loco-lab/hera-led/Solidworks_Assembly/Top Layer.SLDPRT

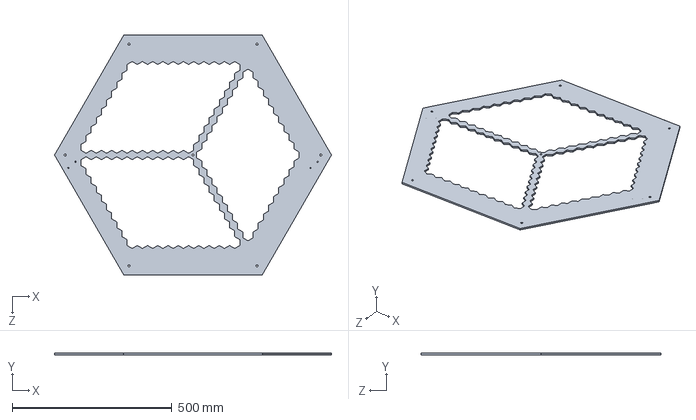
[picture p19: CAD file, 2019-11-21]
Solidworks_Assembly/Top Layer.SLDPRT
866.0 x 4.76 x 750.0 mm
