loco-lab/hera-led/Solidworks_Assembly/6-32 x 0.75in Screw Assy.SLDASM

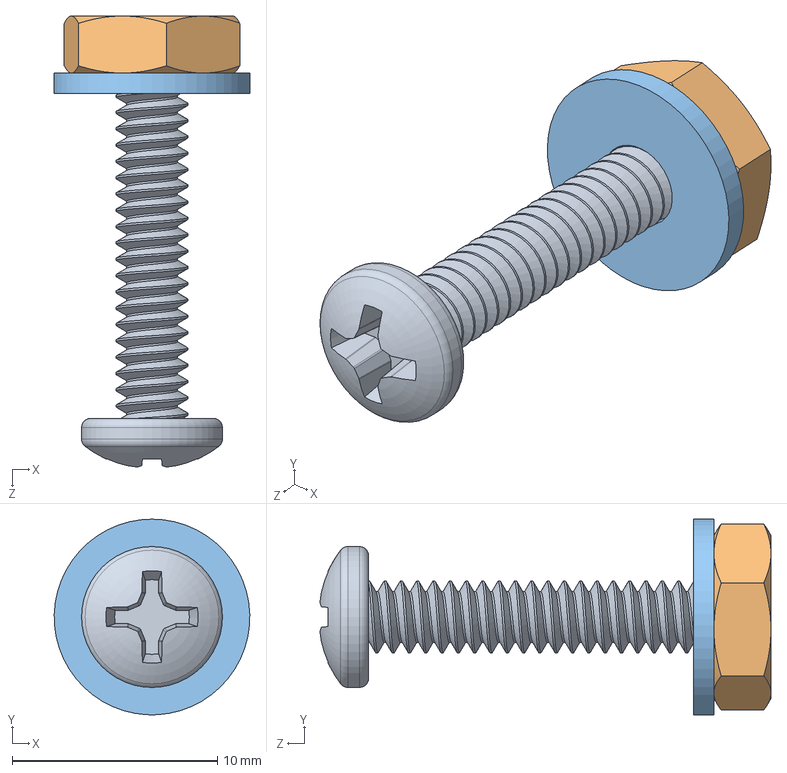
[picture p20: CAD file, 2019-11-21]
Solidworks_Assembly/6-32 x 0.75in Screw Assy.SLDASM
9.52 x 9.53 x 21.9 mm
6-32 x 0.75in Screw
6-32 Nut
6-32 Washer
