loco-lab/hera-led/HERAtest.py

#!/usr/bin/env python3
#Author: Mickey Horn
#custom code testing for HERA LED model

import time
from neopixel import *
import argparse
import pandas as pd
import numpy as np
from datetime import datetime
import math
import random
import matplotlib.pyplot as plt
import matplotlib.colors as clr
import urllib2

parser = argparse.ArgumentParser()
parser.add_argument('-c', '--clear', action='store_true', help='clear the display on exit')
args = parser.parse_args()

# LED strip configuration:
LED_COUNT      = 320     # Number of LED pixels.
LED_PIN        = 18      # GPIO pin connected to the pixels (18 uses PWM!).
LED_FREQ_HZ    = 800000  # LED signal frequency in hertz (usually 800khz)
LED_DMA        = 10      # DMA channel to use for generating signal (try 10)
LED_BRIGHTNESS = 55     # Set to 0 for darkest and 255 for brightest
LED_INVERT     = False   # True to invert the signal (when using NPN transistor level shift)
LED_CHANNEL    = 0       # set to '1' for GPIOs 13, 19, 41, 45 or 53

# Correlates the antenna number defined by HERA to the LED number in the sequential string. Antenna#:LED#
scheme = {
    0:10, 1:9, 2:8, 3:7, 4:6, 5:5, 6:4, 7:3, 8:2, 9:1, 10:0,
    11:11, 12:12, 13:13, 14:14, 15:15, 16:16, 17:17, 18:18, 19:19, 20:20, 21:21,
    22:119,
    23:32, 24:31, 25:30, 26:29, 27:28, 28:27, 29:26, 30:25, 31:24, 32:23, 33:22,
    34:118, 35:120,
    36:33, 37:34, 38:35, 39:36, 40:37, 41:38, 42:39, 43:40, 44:41, 45:42, 46:43,
    47:117, 48:121, 49:139,
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

sec_ring = [214,213,212,211,210,209,208,207,206,205,204,203,202,201,200,199,180,179,160,159,140,139,120,119,0,1,2,3,4,5,6,7,8,9,10,11,32,33,54,55,76,77,98,99,309,308,287,286,265,264,243,242,221,220,219,218,217,216,215]

hours_dict = { # correlates the hour with the hour hand position
    '00':hourhand12, '12':hourhand12,
    '01':hourhand01, '13':hourhand01,
    '02':hourhand02, '14':hourhand02,
    '03':hourhand03, '15':hourhand03,
    '04':hourhand04, '16':hourhand04,
    '05':hourhand05, '17':hourhand05,
    '06':hourhand06, '18':hourhand06,
    '07':hourhand07, '19':hourhand07,
    '08':hourhand08, '20':hourhand08,
    '09':hourhand09, '21':hourhand09,
    '10':hourhand10, '22':hourhand10,
    '11':hourhand11, '23':hourhand11
}

mins_dict = { # correlates the minute with the hour/minute hand position
    '00':hourhand12, '01':hourhand12, '02':hourhand12, '03':hourhand12, '04':hourhand12,
    '05':hourhand01, '06':hourhand01, '07':hourhand01, '08':hourhand01, '09':hourhand01,
    '10':hourhand02, '11':hourhand02, '12':hourhand02, '13':hourhand02, '14':hourhand02,
    '15':hourhand03, '16':hourhand03, '17':hourhand03, '18':hourhand03, '19':hourhand03,
    '20':hourhand04, '21':hourhand04, '22':hourhand04, '23':hourhand04, '24':hourhand04,
    '25':hourhand05, '26':hourhand05, '27':hourhand05, '28':hourhand05, '29':hourhand05,
    '30':hourhand06, '31':hourhand06, '32':hourhand06, '33':hourhand06, '34':hourhand06,
    '35':hourhand07, '36':hourhand07, '37':hourhand07, '38':hourhand07, '39':hourhand07,
    '40':hourhand08, '41':hourhand08, '42':hourhand08, '43':hourhand08, '44':hourhand08,
    '45':hourhand09, '46':hourhand09, '47':hourhand09, '48':hourhand09, '49':hourhand09,
    '50':hourhand10, '51':hourhand10, '52':hourhand10, '53':hourhand10, '54':hourhand10,
    '55':hourhand11, '56':hourhand11, '57':hourhand11, '58':hourhand11, '59':hourhand11
}

secs_dict = { # correlates the second with a point on the edge
    '00':214, '01':213, '02':212, '03':211, '04':210,
    '05':209, '06':208, '07':207, '08':206, '09':205,
    '10':204, '11':203, '12':202, '13':201, '14':200,
    '15':199, '16':180, '17':179, '18':160, '19':159,
    '20':140, '21':139, '22':120, '23':119, '24':0,
    '25':1, '26':2, '27':3, '28':4, '29':5,
    '30':6, '31':7, '32':8, '33':9, '34':10,
    '35':11, '36':32, '37':33, '38':54, '39':55,
    '40':76, '41':77, '42':98, '43':99, '44':309,
    '45':308, '46':287, '47':286, '48':265, '49':264,
    '50':243, '51':242, '52':221, '53':220, '54':219,
    '55':218, '56':217, '57':216, '58':215, '59':215
}

hera_h = [288,311,101,78,312,313,290,103,80]
hera_e = [293,294,295,316,317,106,83,84,85]
hera_r = [149,131,127,113,151,152,153,146,133,134,135]
hera_a = [195,184,175,164,156,196,197,198,180,176,182]
hera_text = [hera_h,hera_e,hera_r,hera_a]

# colors
red = [255,0,0]
orange = [255,127,0]
yellow = [255,255,0]
lime = [127,255,0]
green = [0,255,0]
turq = [0,255,127]
cyan = [0,255,255]
teal = [0,127,255]
blue = [0,0,255]
indigo = [127,0,255]
purple = [255,0,255]
pink = [255,0,127]
white = [255,255,255]
off = [0,0,0]
rgbcolors = [red,green,blue]
rainbowcolors = [red,orange,yellow,green,blue,purple]
ringcolors = [red,orange,yellow,lime,green,turq,cyan,blue,indigo,purple,pink]

def clear():
# Turns off all LEDs.
    for i in range(LED_COUNT): strip.setPixelColorRGB(i,0,0,0)
    strip.show()

def pulse(lights,r,g,b,scale):
# Makes a list of lights "breathe".
    for i in list(reversed(np.arange(scale))) + list(np.arange(scale)):
        for j in lights: strip.setPixelColorRGB(j,int(r*(i/float(scale))),int(g*(i/float(scale))),int(b*(i/float(scale))))
        strip.show()
    time.sleep(1)

def flash(lights,r,g,b,ontime,offtime):
# Makes a list of lights turn off and on rapidly.
    for i in lights: strip.setPixelColorRGB(i,r,g,b)
    strip.show()
    time.sleep(ontime)
    for i in lights: strip.setPixelColorRGB(i,0,0,0)
    strip.show()
    time.sleep(offtime)

def next_shape(shapes,colors,direction):
# Takes in a list of "shapes" (lists of LED indices) and a list of colors, and rotates the colors to the next shape once.
# The direction should be 1 or -1, and simply controls which way the colors progress.
# The list of shapes and the list of colors must be the same length.
    for i in range(LED_COUNT):
        for j,k in enumerate(shapes):
            if i in k: strip.setPixelColorRGB(i,colors[j][0],colors[j][1],colors[j][2])
    strip.show()
    colors = colors[direction::] + colors[:direction:]
    return colors

def moving_shapes(shapes,colors,direction,waittime):
# Takes in a list of shapes and a list of colors and cycles the colors through the shapes repeatedly.
# See next_shape() for more detail.
    print('Displaying Moving Shapes')
    for i in range(len(colors)):
        print('Position '+str(i+1))
        colors = next_shape(shapes,colors,direction)
        time.sleep(waittime)

def pumpkin(waittime):
# Displays a Jack-O-Lantern face, spooky!
    print('Displaying Pumpkin')
    for i in range(LED_COUNT):
        if i in pumpkin_face: strip.setPixelColorRGB(i,25,25,25)
        elif i in pumpkin_stem: strip.setPixelColorRGB(i,0,255,0)
        else: strip.setPixelColorRGB(i,255,65,0)
    strip.show()
    time.sleep(waittime)

def random_colors():
# Sets each antenna to a random color.
    for i in range(LED_COUNT): strip.setPixelColorRGB(i,random.randrange(0,255,1),random.randrange(0,255,1),random.randrange(0,255,1))
    strip.show()
    time.sleep(2)

def ant_sequence():
# Loops through all lights in antenna order and sets them to R>G>B.
    print('Displaying Antenna Sequences')
    clear()
    print('Loop 1')
    for i in range(LED_COUNT):
        strip.setPixelColorRGB(scheme[i],255,0,0)
        strip.show()
    print('Loop 2')
    for i in range(LED_COUNT):
        strip.setPixelColorRGB(scheme[i],0,255,0)
        strip.show()
    print('Loop 3')
    for i in range(LED_COUNT):
        strip.setPixelColorRGB(scheme[i],0,0,255)
        strip.show()

def ant_status_ew(pulses):
# Reads the live antenna status csv from HERAnow and outputs appropriate colors for each EW antenna.
    print('Displaying Live EW Antenna Status')
    red_lights = []
    status = np.array(pd.read_csv('http://heranow.reionization.org/ant_stats.csv', header=0, names=['Ant','Auto','PAM','ADC','ADC RMS','FEM T','FEM P','EQ']))
    for i in status:
        antname = i[0]
        antnum = int(antname[2:len(antname)-1])
        antdir = antname[len(antname)-1:len(antname)]
        if antdir=='e' and -1<antnum<320:
            if pd.isnull(i[1])==True: strip.setPixelColorRGB(scheme[antnum],255,127,0) # weird nan, orange
            elif i[1]=='CONST': strip.setPixelColorRGB(scheme[antnum],80,0,255) # offline, blue
            elif i[1]=='OFF' : strip.setPixelColorRGB(scheme[antnum],0,0,0) # not built, off
            else:
                if int(float(i[1]))>=15: strip.setPixelColorRGB(scheme[antnum],0,255,0) # good, green
                elif int(float(i[1]))<15:
                    strip.setPixelColorRGB(scheme[antnum],255,50,0) # bad, red
                    red_lights.append(scheme[antnum])
                else: strip.setPixelColorRGB(scheme[antnum],0,0,0) # not in csv, off
    print('Initial Color')
    strip.show()
    counter = 0
    #while counter<pulses:
    #    print('Pulse '+str(counter+1))
    #    pulse(red_lights,125,25,0,50)
    #    counter += 1
    time.sleep(5)

def ant_status_ns(pulses):
# Reads the live antenna status csv from HERAnow and outputs appropriate colors for each NS antenna.
    print('Displaying Live NS Antenna Status')
    red_lights = []
    status = np.array(pd.read_csv('http://heranow.reionization.org/ant_stats.csv', header=0, names=['Ant','Auto','PAM','ADC','ADC RMS','FEM T','FEM P','EQ']))
    for i in status:
        antname = i[0]
        antnum = int(antname[2:len(antname)-1])
        antdir = antname[len(antname)-1:len(antname)]
        if antdir=='n' and -1<antnum<320:
            if pd.isnull(i[1])==True: strip.setPixelColorRGB(scheme[antnum],255,127,0) # weird nan, orange
            elif i[1]=='CONST': strip.setPixelColorRGB(scheme[antnum],80,0,255) # offline, blue
            elif i[1]=='OFF' : strip.setPixelColorRGB(scheme[antnum],0,0,0) # not built, off
            else:
                if int(float(i[1]))>=15: strip.setPixelColorRGB(scheme[antnum],0,255,0) # good, green
                elif int(float(i[1]))<15:
                    strip.setPixelColorRGB(scheme[antnum],255,50,0) # bad, red
                    red_lights.append(scheme[antnum])
                else: strip.setPixelColorRGB(scheme[antnum],0,0,0) # not in csv, off
    print('Initial Color')
    strip.show()
    counter = 0
    #while counter<pulses:
    #    print('Pulse '+str(counter+1))
    #    pulse(red_lights,125,25,0,50)
    #    counter += 1
    time.sleep(5)

def ant_status():
# Reads the live antenna status csv from HERAnow and outputs appropriate colors for each antenna. The worst dipole is always shown.
    print('Displaying Live Antenna Status')
    status = np.array(pd.read_csv('http://heranow.reionization.org/ant_stats.csv', header=0, names=['Ant','Auto','PAM','ADC','ADC RMS','FEM T','FEM P','EQ']))
    e_status = np.empty((0,8))
    n_status = np.empty((0,8))
    for i in status:
        antname = i[0]
        antnum = int(antname[2:len(antname)-1])
        antdir = antname[len(antname)-1:len(antname)]
        if antdir=='e' and -1<antnum<320: e_status = np.append(e_status,[i],axis=0)
        elif antdir=='n' and -1<antnum<320: n_status = np.append(n_status,[i],axis=0)
    for j in range(320):
        if pd.isnull(e_status[j][1])==True or pd.isnull(n_status[j][1])==True: strip.setPixelColorRGB(scheme[j],255,127,0) # weird nan, orange
        elif e_status[j][1]=='CONST' or n_status[j][1]=='CONST': strip.setPixelColorRGB(scheme[j],80,0,255) # offline, blue
        elif e_status[j][1]=='OFF' or n_status[j][1]=='OFF': strip.setPixelColorRGB(scheme[j],0,0,0) # not built, off
        else:
            if int(float(e_status[j][1]))>=15 and int(float(n_status[j][1]))>=15: strip.setPixelColorRGB(scheme[j],0,255,0) # good, green
            elif int(float(e_status[j][1]))<15 or int(float(n_status[j][1]))<15: strip.setPixelColorRGB(scheme[j],255,50,0) # bad, red
            else: strip.setPixelColorRGB(scheme[j],0,0,0) # not in csv, off
    strip.show()
    time.sleep(120)

def colorscale(mag,cmin,cmax):
# Returns a tuple of floats between 0 and 255 for RGB, scaling from green to yellow.
    try: x = float(mag-cmin)/(cmax-cmin) # scales from 0 to 1
    except ZeroDivisionError: x=0.5 # cmax==cmin
    r = int(x*255)
    g = 255
    b = int(75-(x*75))
    return r,g,b

def ant_status_scaling():
# Reads the live antenna status csv from HERAnow and outputs appropriate colors for each antenna. The worst dipole is always shown.
    status = np.array(pd.read_csv('http://heranow.reionization.org/media/ant_stats.csv', header=0, names=['Ant','Pol','Constructed','Node','Fem Switch','Apriori','Spectra','PAM Power','ADC Power','ADC RMS','FEM IMU Theta','FEM IMU Phi','EQ Coeffs']))
    e_status = np.empty((0,13))
    n_status = np.empty((0,13))
    
    for i in status:
        antnum = i[0]
        antpol = i[1]
        print(antnum,antpol)
        if antpol=='e' and -1<antnum<320: e_status = np.append(e_status,[i],axis=0)
        elif antpol=='n' and -1<antnum<320: n_status = np.append(n_status,[i],axis=0)
    print(e_status)
    for j in range(320):
        e_constructed = e_status[j][2]
        n_constructed = n_status[j][2]
        e_spectra = e_status[j][6]
        n_spectra = n_status[j][6]

        if e_constructed==False or n_constructed==False: strip.setPixelColorRGB(scheme[j],0,0,0) # not built, off
        else:
            if pd.isnull(e_spectra)==True or pd.isnull(n_spectra)==True: strip.setPixelColorRGB(scheme[j],0,127,255) # offline, blue
            elif int(float(e_spectra))>=-45 and int(float(n_spectra))>=-45:
                avg_spectra = (float(e_spectra)+float(n_spectra))/2
                r,g,b = colorscale(avg_spectra,-100,-10)
                strip.setPixelColorRGB(scheme[j],r,g,b) #good, scaled green to yellow
            elif int(float(e_spectra))<-45 or int(float(n_spectra))<-45: strip.setPixelColorRGB(scheme[j],255,50,0) # bad, red
            elif int(float(e_spectra))>-20 or int(float(n_spectra))>-20: strip.setPixelColorRGB(scheme[j],255,50,0) # bad, red
            #else: strip.setPixelColorRGB(scheme[j],0,0,0) # not in csv, off

    strip.show()
    seconds = str(datetime.now().time())[6:8]
    for k in sec_ring: strip.setPixelColorRGB(secs_dict[seconds],200,200,200)
    strip.show()    
    time.sleep(.75)
def draw_hera_status(status):
      #input a status array (numpy with columns)
      #draw it on the led board
    e_status = np.empty((0,13))
    n_status = np.empty((0,13))
    for i in status:
        antnum = i[0]
        antpol = i[1]
        if antpol=='e' and -1<antnum<320: e_status = np.append(e_status,[i],axis=0)
        elif antpol=='n' and -1<antnum<320: n_status = np.append(n_status,[i],axis=0)

    for j in range(320):
        e_constructed = e_status[j][2]
        n_constructed = n_status[j][2]
        e_spectra = e_status[j][6]
        n_spectra = n_status[j][6]

        if e_constructed==False or n_constructed==False: strip.setPixelColorRGB(scheme[j],0,0,0) # not built, off
        else:
            if pd.isnull(e_spectra)==True or pd.isnull(n_spectra)==True: strip.setPixelColorRGB(scheme[j],0,127,255) # offline, blue
            elif int(float(e_spectra))>=-45 and int(float(n_spectra))>=-45:
                avg_spectra = (float(e_spectra)+float(n_spectra))/2
                r,g,b = colorscale(avg_spectra,-100,-10)
                strip.setPixelColorRGB(scheme[j],r,g,b) #good, scaled green to yellow
            elif int(float(e_spectra))<-45 or int(float(n_spectra))<-45: strip.setPixelColorRGB(scheme[j],255,50,0) # bad, red
            elif int(float(e_spectra))>-20 or int(float(n_spectra))>-20: strip.setPixelColorRGB(scheme[j],255,50,0) # bad, red
            #else: strip.setPixelColorRGB(scheme[j],0,0,0) # not in csv, off

            strip.show()
def draw_time_dot():
    #put a dot on the edge of the HERA board to indicate seconds.
    seconds = str(datetime.now().time())[6:8]
    for k in sec_ring: 
        strip.setPixelColorRGB(secs_dict[seconds],200,200,200)
def get_hera_status():
     return np.array(pd.read_csv('http://heranow.reionization.org/media/ant_stats.csv', 
                   header=0, 
                    names=['Ant','Pol','Constructed','Node','Fem Switch',
                    'Apriori','Spectra','PAM Power','ADC Power','ADC RMS',
                    'FEM IMU Theta','FEM IMU Phi','EQ Coeffs']))
def ant_status_scaling_test(status):
# Reads the live antenna status csv from HERAnow and outputs appropriate colors for each antenna. The worst dipole is always shown.
# only reads the status at the top of the minute
    #status = np.empty((700,13))
    connection_error=False
    seconds = str(datetime.now().time())[6:8]
    e_status = np.empty((0,13))
    n_status = np.empty((0,13))
    if seconds == '00':  
        try:
            status = np.array(pd.read_csv('http://heranow.reionization.org/media/ant_stats.csv', 
                   header=0, 
                    names=['Ant','Pol','Constructed','Node','Fem Switch',
                    'Apriori','Spectra','PAM Power','ADC Power','ADC RMS',
                    'FEM IMU Theta','FEM IMU Phi','EQ Coeffs']))
        except(urllib2.URLError):
            print("connection error")
            connection_error = True
    for i in status:
        antnum = i[0]
        antpol = i[1]
        if antpol=='e' and -1<antnum<320: e_status = np.append(e_status,[i],axis=0)
        elif antpol=='n' and -1<antnum<320: n_status = np.append(n_status,[i],axis=0)
    try:
        for j in range(320):
            e_constructed = e_status[j][2]
            n_constructed = n_status[j][2]
            e_spectra = e_status[j][6]
            n_spectra = n_status[j][6]

            if e_constructed==False or n_constructed==False: strip.setPixelColorRGB(scheme[j],0,0,0) # not built, off
            else:
                if pd.isnull(e_spectra)==True or pd.isnull(n_spectra)==True: strip.setPixelColorRGB(scheme[j],0,127,255) # offline, blue
                elif int(float(e_spectra))>=-45 and int(float(n_spectra))>=-45:
                    avg_spectra = (float(e_spectra)+float(n_spectra))/2
                    r,g,b = colorscale(avg_spectra,-100,-10)
                    strip.setPixelColorRGB(scheme[j],r,g,b) #good, scaled green to yellow
                elif int(float(e_spectra))<-45 or int(float(n_spectra))<-45: strip.setPixelColorRGB(scheme[j],255,50,0) # bad, red
                elif int(float(e_spectra))>-20 or int(float(n_spectra))>-20: strip.setPixelColorRGB(scheme[j],255,50,0) # bad, red
                #else: strip.setPixelColorRGB(scheme[j],0,0,0) # not in csv, off

                strip.show()
    except(IndexError):
        print("cant even")
    seconds = str(datetime.now().time())[6:8]
    #for k in sec_ring: strip.setPixelColorRGB(secs_dict[seconds],200,200,200)
    if connection_error:
        strip.setPixelColorRGB(secs_dict[seconds],255,0,0)
    else:
        strip.setPixelColorRGB(secs_dict[seconds],200,200,200)
    strip.show()    
    time.sleep(.75)
    return status

def adopt_antenna():
# A fun outreach demo, let kids choose and color an antenna to make a collage by the end!
    print(' ')
    print('It is time to adopt your very own HERA antenna!')
    antenna = int(input('Which antenna would you like? Pick any number between 0 and 319: '))
    while antenna<0 or antenna>319: antenna = int(input('Oops! Which antenna would you like? Pick any number between 0 and 319: '))
    red = int(input('How much red do you want? Enter a number between 0 (no red) and 255 (max red): '))
    while red<0 or red>255: red = int(input('Oops! How much red do you want? Enter a number between 0 (no red) and 255 (max red): '))
    green = int(input('How much green do you want? Enter a number between 0 and 255: '))
    while green<0 or green>255: green = int(input('Oops! How much green do you want? Enter a number between 0 and 255: '))
    blue = int(input('How much blue do you want? Enter a number between 0 and 255: '))
    while blue<0 or blue>255: blue = int(input('Oops! How much blue do you want? Enter a number between 0 and 255: '))
    strip.setPixelColorRGB(scheme[antenna],red,green,blue)
    strip.show()
    print('Your antenna is on! Can you find it?')
    print('-------------------------')
    time.sleep(10)

def clock():
# A real time analog clock, with 3 hands!
    print('Displaying Clock')
    nowtime = str(datetime.now().time()) #format is hh:mm:ss.ssssss
    hours = nowtime[0:2]
    minutes = nowtime[3:5]
    seconds = nowtime[6:8]
    print('It is currently '+hours+':'+minutes+':'+seconds)
    clear()
    minutehand = mins_dict[minutes]
    for i in minutehand: strip.setPixelColorRGB(i,0,255,0)
    hourhand = hours_dict[hours][:int(round(len(hours_dict[hours])/2)+1)]
    for i in hourhand: strip.setPixelColorRGB(i,0,0,255)
    for i in sec_ring[:len(sec_ring)-(59-int(seconds))]: strip.setPixelColorRGB(i,255,0,0) # enable this line for cumulative seconds ring
    #strip.setPixelColorRGB(secs_dict[seconds],255,0,0) # enable this line for 1 second dot at a time
    strip.show()
    time.sleep(.97)

def hera():
# Displays the text "HERA".
    print('Displaying HERA')
    for i in range(LED_COUNT):
        if i in hera_h: strip.setPixelColorRGB(i,0,0,255)
        elif i in hera_e: strip.setPixelColorRGB(i,255,0,0)
        elif i in hera_r: strip.setPixelColorRGB(i,0,255,0)
        elif i in hera_a: strip.setPixelColorRGB(i,255,255,0)
        else: strip.setPixelColorRGB(i,0,0,0)
    strip.show()
    time.sleep(10)

def image_mapper(file):
    image_map = np.array(pd.read_csv(file, header=0, names=['r','g','b']))
    for i in range(len(image_map)): strip.setPixelColorRGB(i,int(image_map[i][0]),int(image_map[i][1]),int(image_map[i][2]))
    strip.show()
    time.sleep(60)


# main code
print('Starting')
strip = Adafruit_NeoPixel(LED_COUNT, LED_PIN, LED_FREQ_HZ, LED_DMA, LED_INVERT, LED_BRIGHTNESS, LED_CHANNEL)
strip.begin()

try:
    status = np.empty((700,13))
    while True:
        #moving_shapes(sixths,rainbowcolors,-1,.1)
        #moving_shapes(sixths,rainbowcolors,-1,.1)

        #moving_shapes(rings,ringcolors,1,.1)
        #moving_shapes(rings,ringcolors,-1,.1)

        pumpkin(0)

        #random_colors()

        #ant_sequence()

        #ant_status_ew(3)
        #ant_status_ns(3)
        #status = ant_status_scaling_test(status)
        #ant_status_scaling()
        #adopt_antenna()

        #clock()
        time.sleep(5)

        #hera()

        #image_mapper('treergb')
        #seconds = str(datetime.now().time())[6:8]
        #if seconds=='00':
        #    status = get_hera_status()
        #draw_hera_status(status)
        #draw_time_dot()
        #time.sleep(60)


except KeyboardInterrupt:
    if args.clear:
        print('Clear')
        clear()
